picolemon/picocom16/sw/demos/gfx_demo/assets/models/trex/T_Rex_1_FBX_LOW_1001_AlbedoTransparency.png

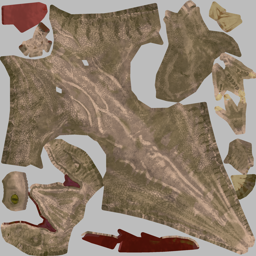
sw/demos/gfx_demo/assets/models/trex/T_Rex_1_FBX_LOW_1001_AlbedoTransparency.png
